psp20/Hardware/Dokumentation/Anleitung/Bilder/IO_Sw_FT232.jpg

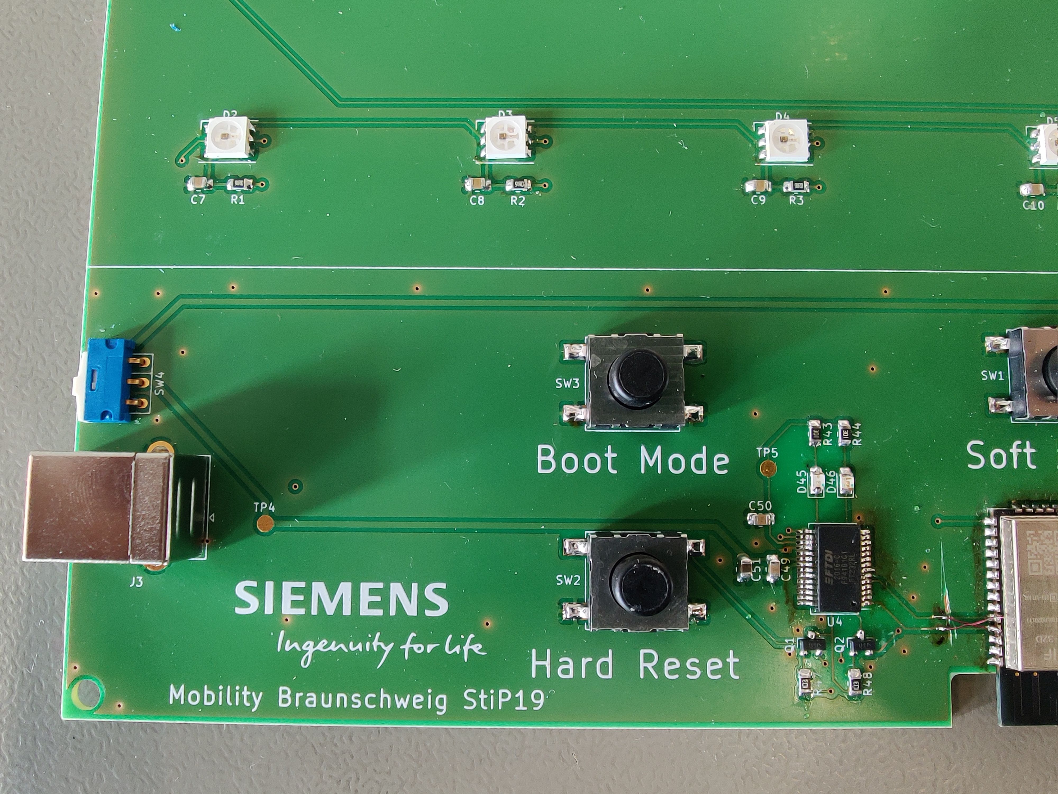
Dokumentation/Anleitung/Bilder/IO_Sw_FT232.jpg
