psp20/Hardware/Dokumentation/Anleitung/Bilder/LEDs.jpg

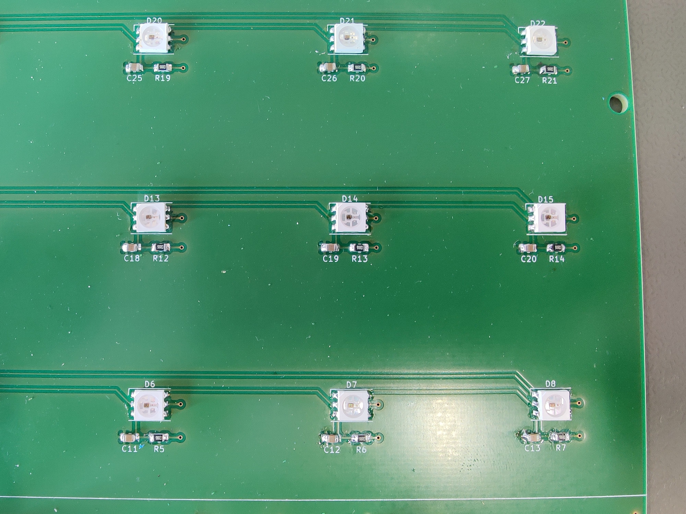
Dokumentation/Anleitung/Bilder/LEDs.jpg
