psp20/Hardware/Dokumentation/Anleitung/Bilder/Sw_ESP_LEDs.jpg

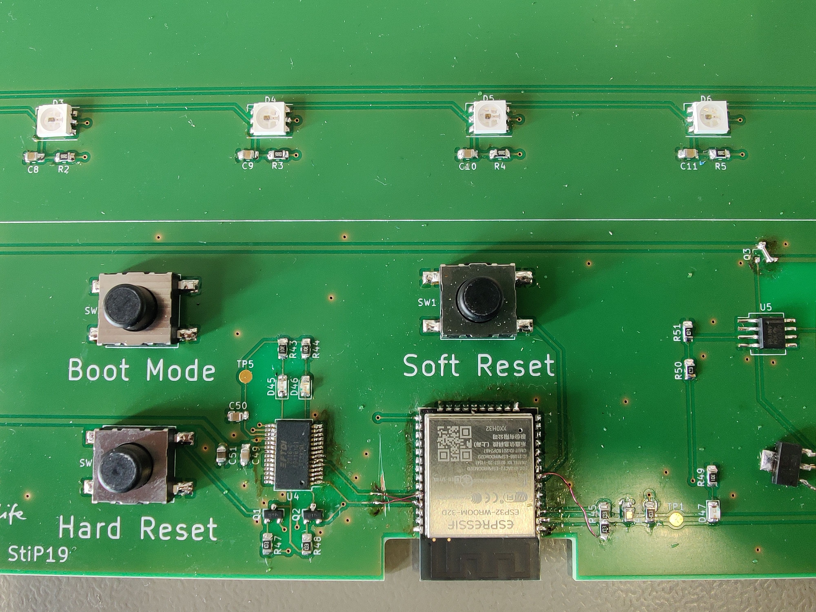
Dokumentation/Anleitung/Bilder/Sw_ESP_LEDs.jpg
